cab404/ploopy-mods/headband/export/band+coils=....0+th=....2+r=...30.stl

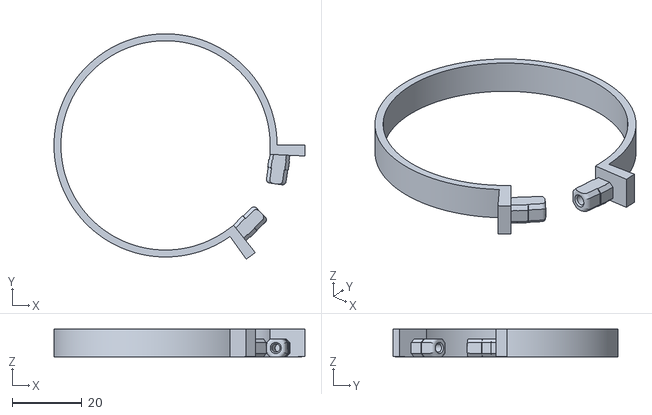
[picture p19: CAD file, 2024-08-13]
headband/export/band+coils=....0+th=....2+r=...30.stl
72.0 x 64.6 x 8.00
