cab404/ploopy-mods/headband/export/band+coils=...15+th=....2+r=...40.stl

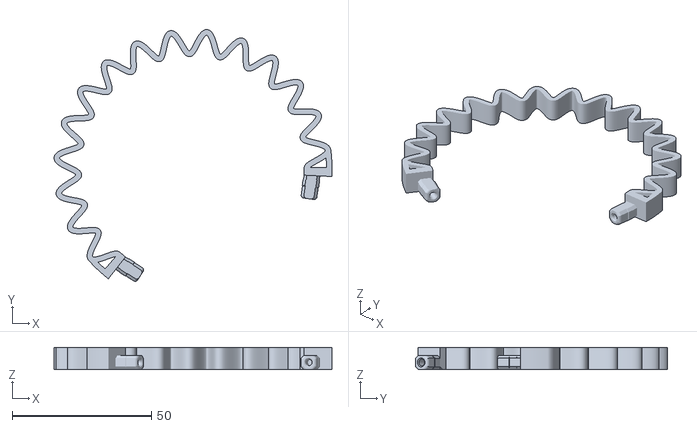
[picture p20: CAD file, 2024-08-13]
headband/export/band+coils=...15+th=....2+r=...40.stl
99.9 x 90.5 x 8.00
