cab404/ploopy-mods/headband/export/band+coils=....0+th=....2+r=...90.stl

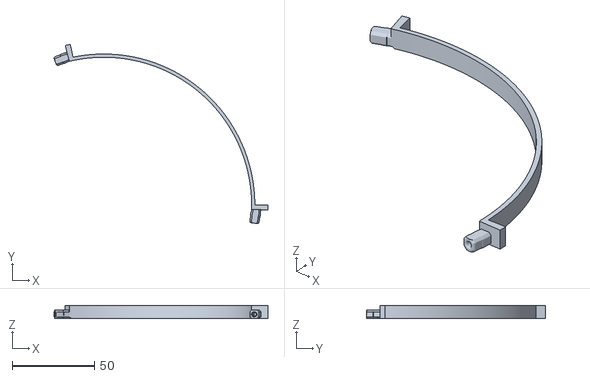
[picture p22: CAD file, 2024-08-13]
headband/export/band+coils=....0+th=....2+r=...90.stl
130.3 x 109.2 x 8.00
