cab404/ploopy-mods/headband/export/band+coils=....9+th=....2+r=...40.stl

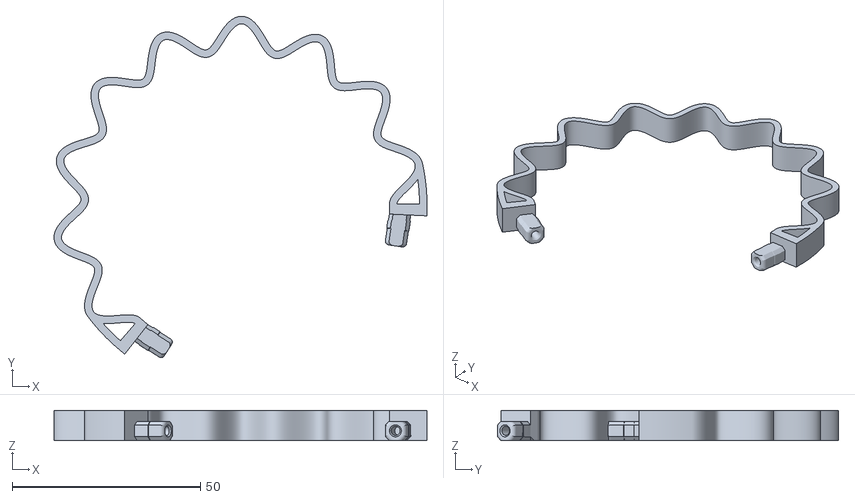
[picture p28: CAD file, 2024-08-13]
headband/export/band+coils=....9+th=....2+r=...40.stl
99.2 x 90.7 x 8.00
