cab404/ploopy-mods/headband/export/band+coils=...15+th=....4+r=...50.stl

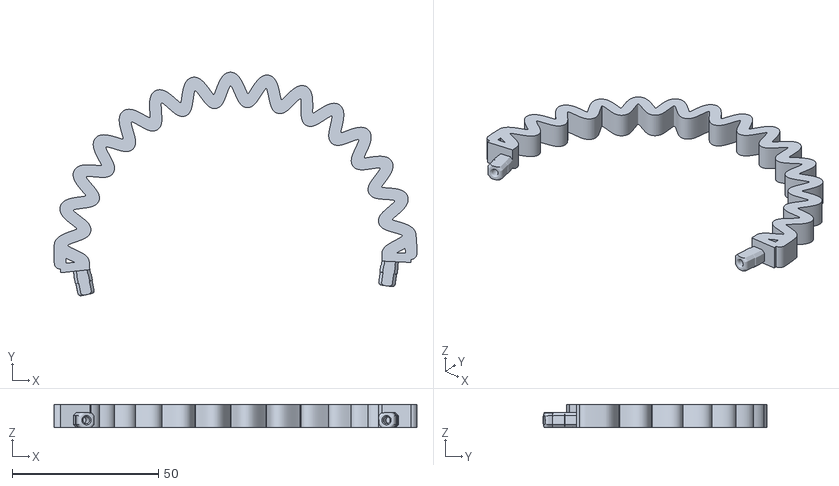
[picture p31: CAD file, 2024-08-13]
headband/export/band+coils=...15+th=....4+r=...50.stl
124.0 x 76.4 x 8.00
