cab404/ploopy-mods/headband/export/band+coils=....9+th=....2+r=...70.stl

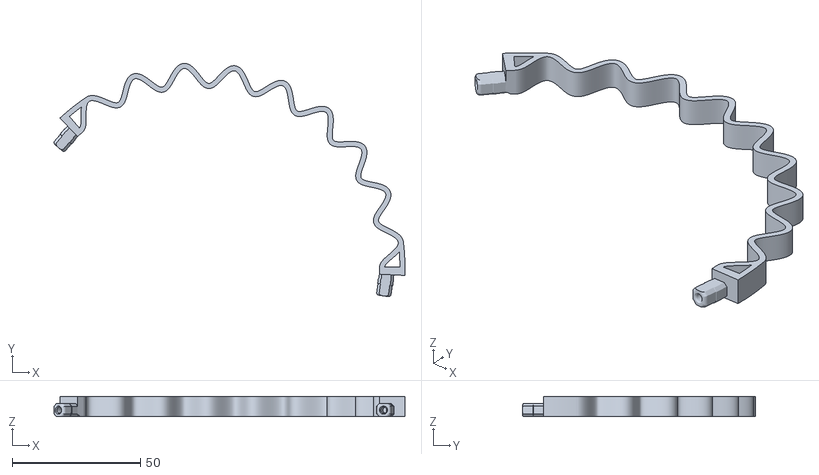
[picture p32: CAD file, 2024-08-13]
headband/export/band+coils=....9+th=....2+r=...70.stl
137.0 x 91.1 x 8.00
