cab404/ploopy-mods/newcap/export/newcap+magnet_size=..4.8+open=..yes+h=..1.9+layer_height=..0.1.stl

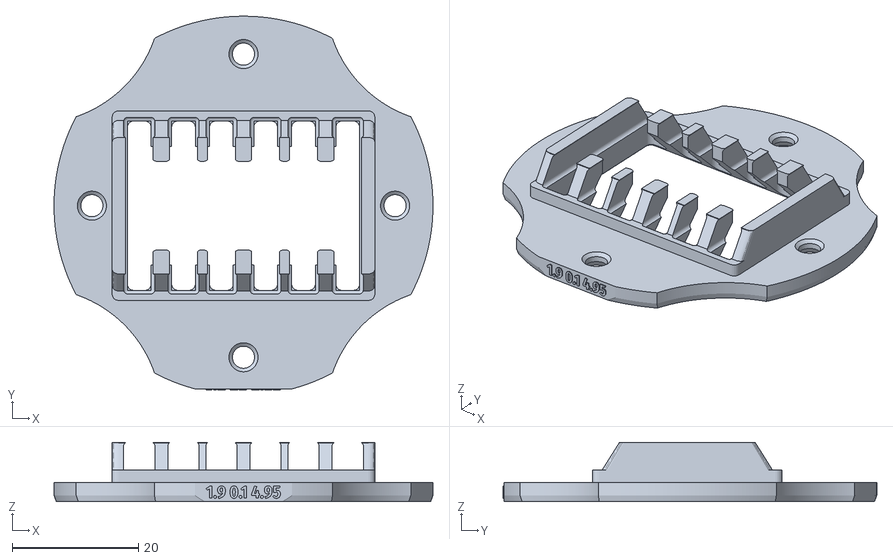
[picture p33: CAD file, 2024-08-13]
newcap/export/newcap+magnet_size=..4.8+open=..yes+h=..1.9+layer_height=..0.1.stl
60.0 x 59.1 x 9.40
