cab404/ploopy-mods/headband/export/band+coils=...15+th=....4+r=...90.stl

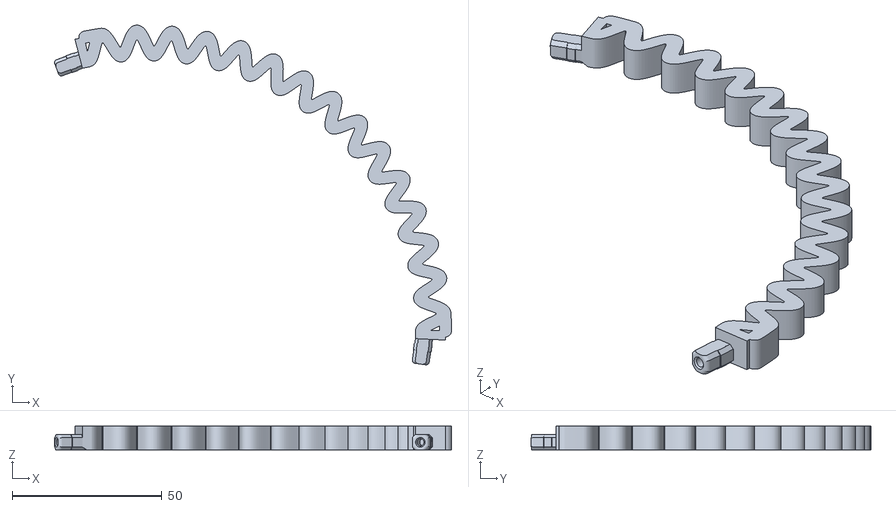
[picture p36: CAD file, 2024-08-13]
headband/export/band+coils=...15+th=....4+r=...90.stl
132.3 x 113.3 x 8.00
