cab404/ploopy-mods/headband/export/band+coils=....9+th=....4+r=...70.stl

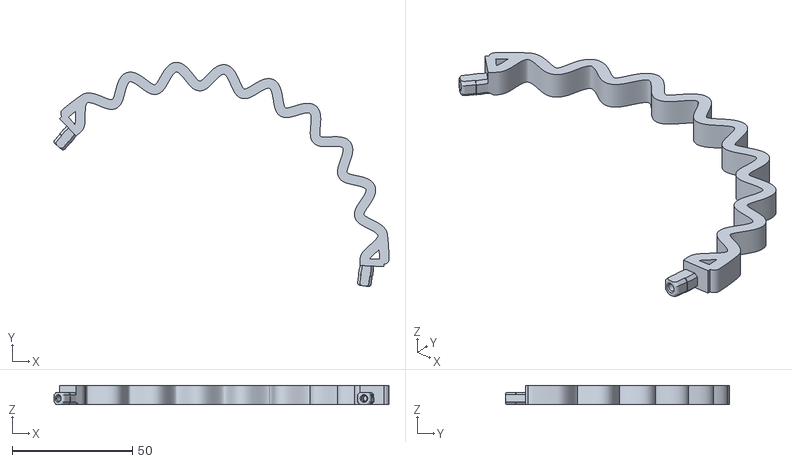
[picture p38: CAD file, 2024-08-13]
headband/export/band+coils=....9+th=....4+r=...70.stl
139.0 x 93.1 x 8.00
