cab404/ploopy-mods/headband/export/band+coils=....5+th=....2+r=...40.stl

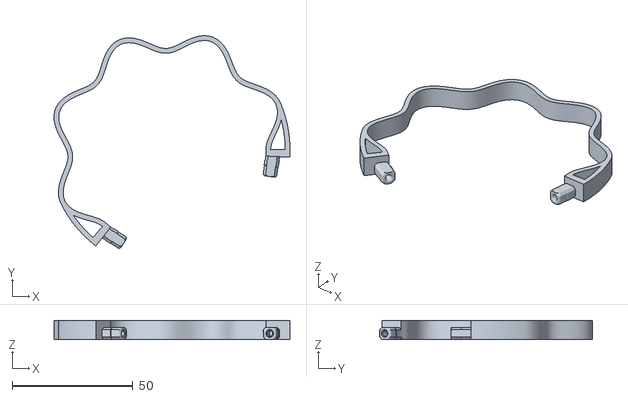
[picture p39: CAD file, 2024-08-13]
headband/export/band+coils=....5+th=....2+r=...40.stl
97.7 x 88.0 x 8.00
