cab404/ploopy-mods/newcap/export/newcap+magnet_size=..4.5+open=..yes+h=..1.8+layer_height=..0.2.stl

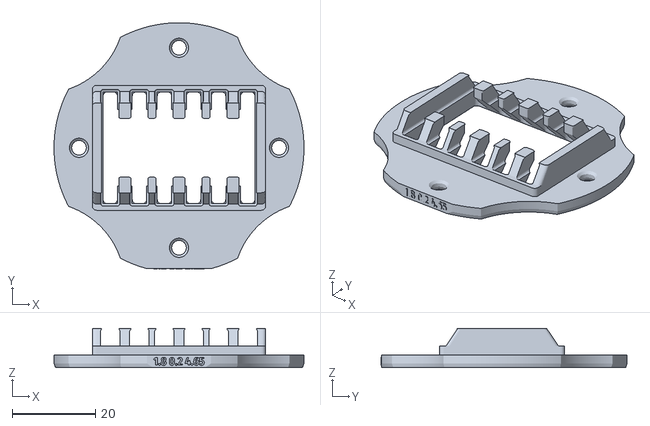
[picture p40: CAD file, 2024-08-13]
newcap/export/newcap+magnet_size=..4.5+open=..yes+h=..1.8+layer_height=..0.2.stl
60.0 x 59.1 x 9.40
