cab404/ploopy-mods/headband/export/band+coils=....1+th=....2+r=...30.stl

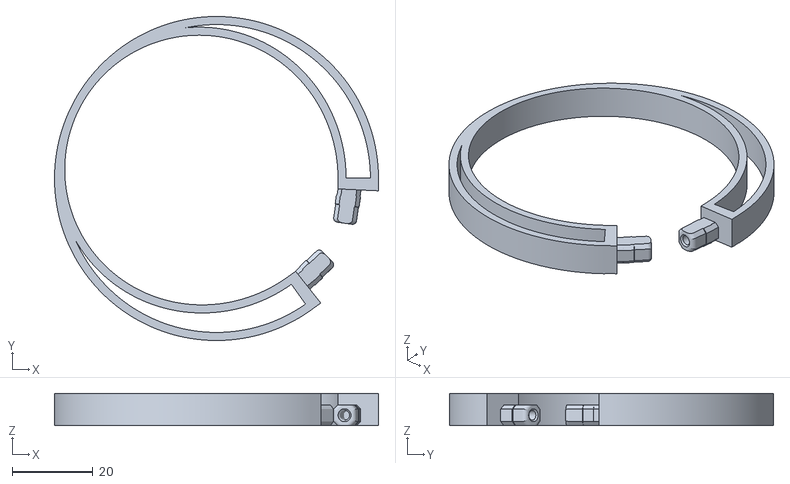
[picture p41: CAD file, 2024-08-13]
headband/export/band+coils=....1+th=....2+r=...30.stl
80.0 x 80.0 x 8.00
