cab404/ploopy-mods/headband/export/band+coils=....9+th=....2+r=...50.stl

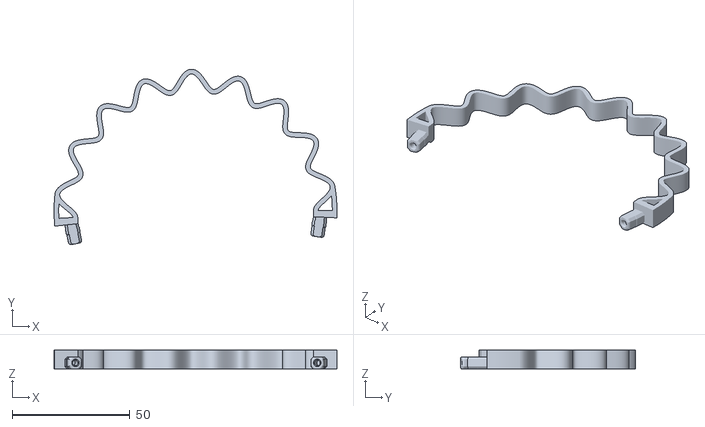
[picture p42: CAD file, 2024-08-13]
headband/export/band+coils=....9+th=....2+r=...50.stl
120.0 x 74.4 x 8.00
