cab404/ploopy-mods/newcap/export/newcap+magnet_size=..4.5+open=..yes+h=..1.6+layer_height=..0.1.stl

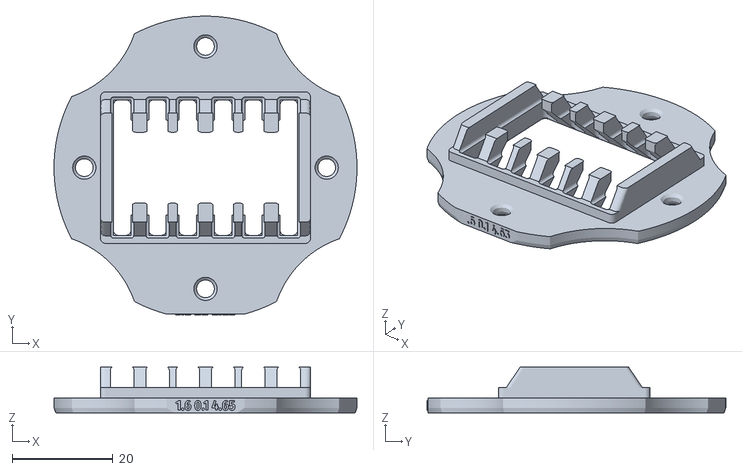
[picture p43: CAD file, 2024-08-13]
newcap/export/newcap+magnet_size=..4.5+open=..yes+h=..1.6+layer_height=..0.1.stl
60.0 x 59.1 x 9.10
