cab404/ploopy-mods/headband/export/band+coils=....5+th=....2+r=...70.stl

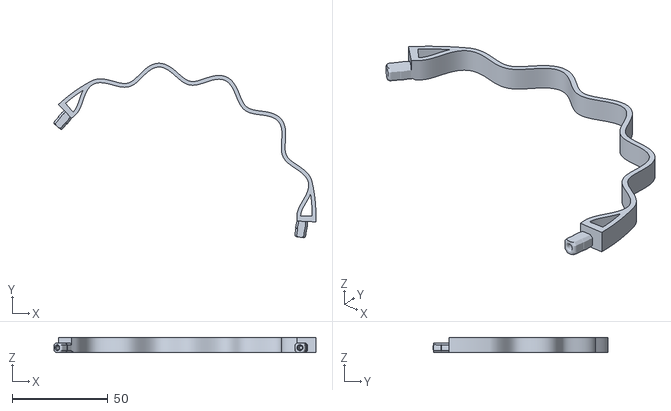
[picture p44: CAD file, 2024-08-13]
headband/export/band+coils=....5+th=....2+r=...70.stl
137.0 x 91.3 x 8.00
