cab404/ploopy-mods/headband/export/band+coils=....0+th=....2+r=...40.stl

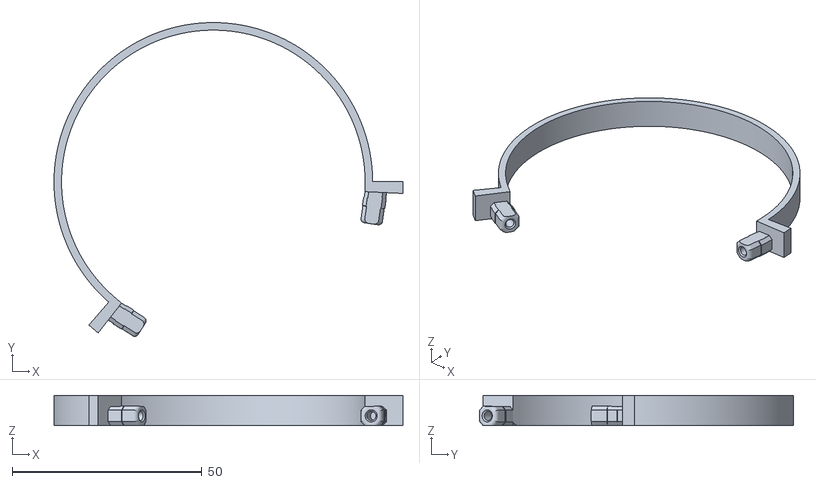
[picture p45: CAD file, 2024-08-13]
headband/export/band+coils=....0+th=....2+r=...40.stl
92.0 x 82.7 x 8.00
