cab404/ploopy-mods/headband/export/band+coils=....0+th=....2+r=...50.stl

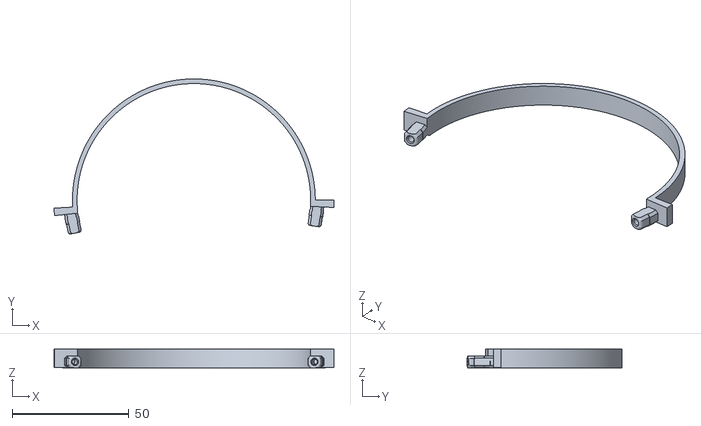
[picture p47: CAD file, 2024-08-13]
headband/export/band+coils=....0+th=....2+r=...50.stl
119.9 x 66.4 x 8.00
