cab404/ploopy-mods/headband/export/band+coils=....1+th=....4+r=...70.stl

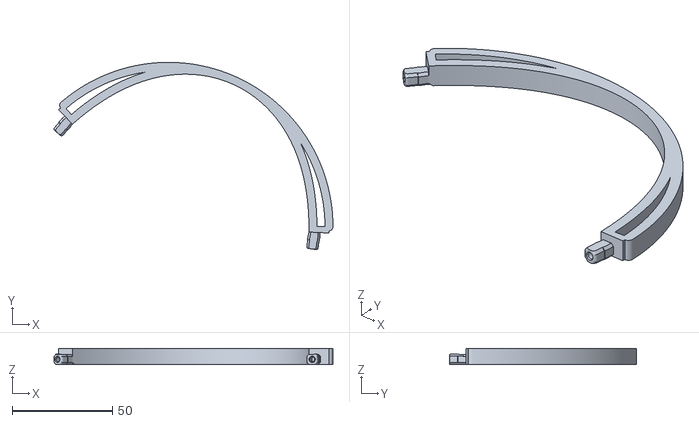
[picture p49: CAD file, 2024-08-13]
headband/export/band+coils=....1+th=....4+r=...70.stl
139.0 x 93.3 x 8.00
