cab404/ploopy-mods/headband/export/band+coils=....9+th=....2+r=...30.stl

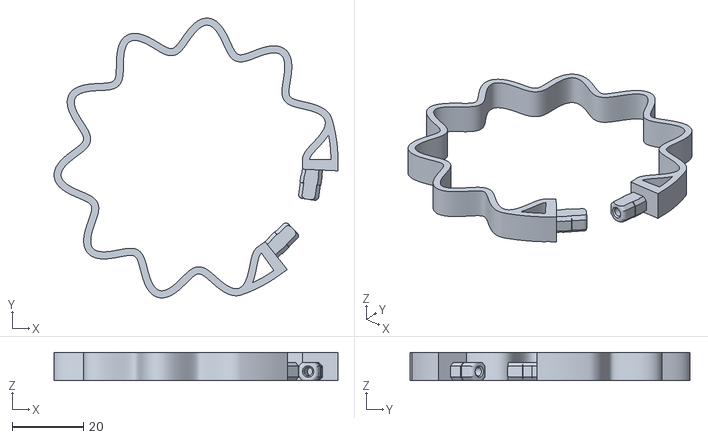
[picture p51: CAD file, 2024-08-13]
headband/export/band+coils=....9+th=....2+r=...30.stl
79.8 x 78.6 x 8.00
