cab404/ploopy-mods/headband/export/band+coils=....9+th=....4+r=...30.stl

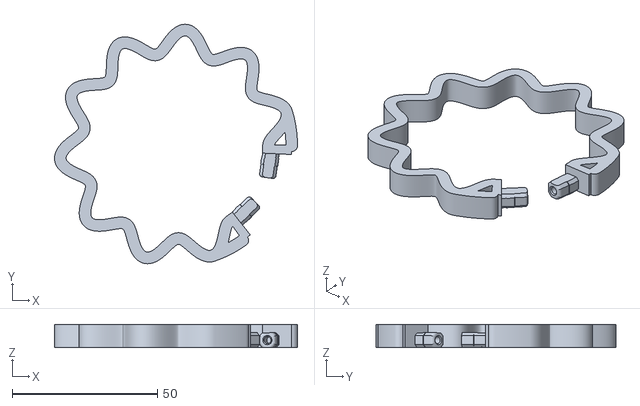
[picture p52: CAD file, 2024-08-13]
headband/export/band+coils=....9+th=....4+r=...30.stl
83.7 x 82.5 x 8.00
