cab404/ploopy-mods/headband/export/band+coils=...15+th=....2+r=...30.stl

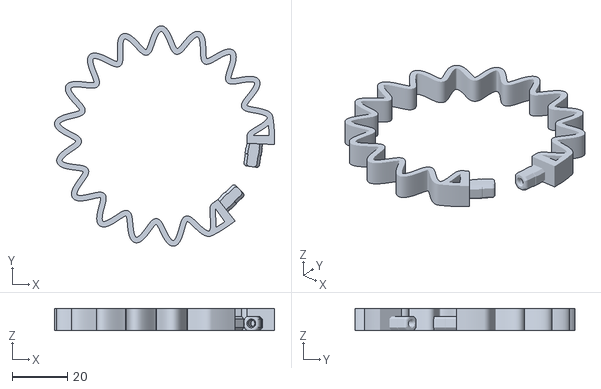
[picture p54: CAD file, 2024-08-13]
headband/export/band+coils=...15+th=....2+r=...30.stl
79.7 x 79.8 x 8.00
