cab404/ploopy-mods/headband/export/band+coils=....0+th=....4+r=...50.stl

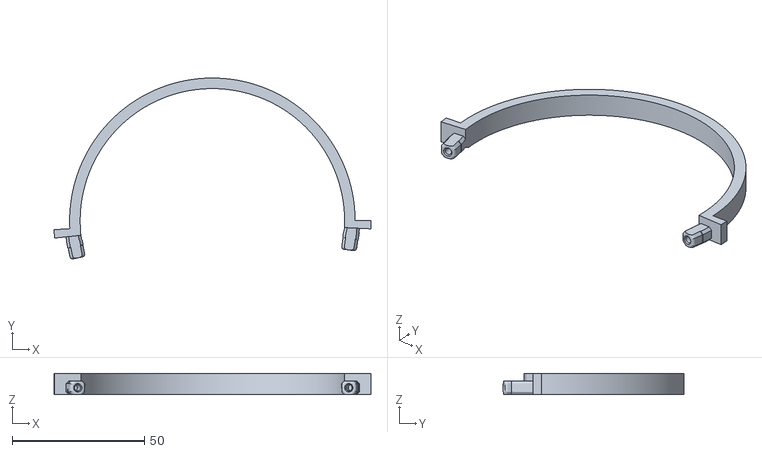
[picture p55: CAD file, 2024-08-13]
headband/export/band+coils=....0+th=....4+r=...50.stl
119.9 x 68.4 x 8.00
