cab404/ploopy-mods/headband/export/band+coils=....9+th=....2+r=...90.stl

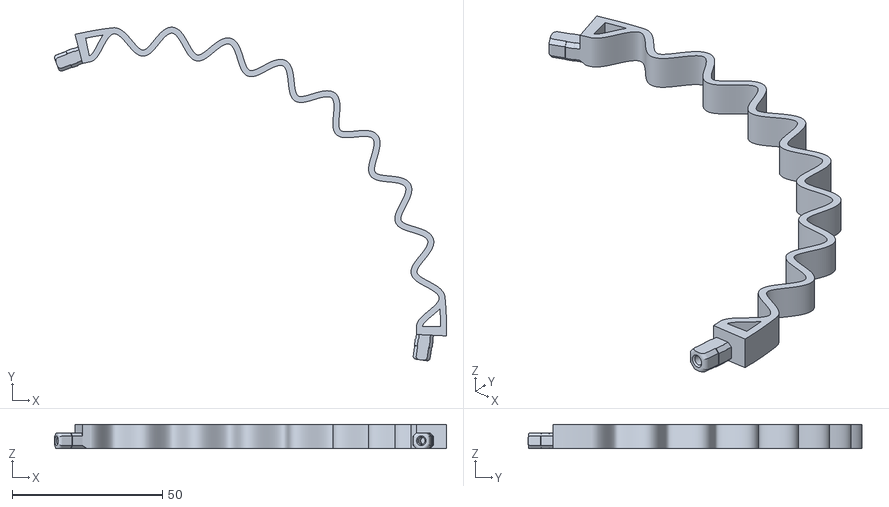
[picture p56: CAD file, 2024-08-13]
headband/export/band+coils=....9+th=....2+r=...90.stl
130.3 x 110.9 x 8.00
