cab404/ploopy-mods/headband/export/band+coils=....1+th=....2+r=...40.stl

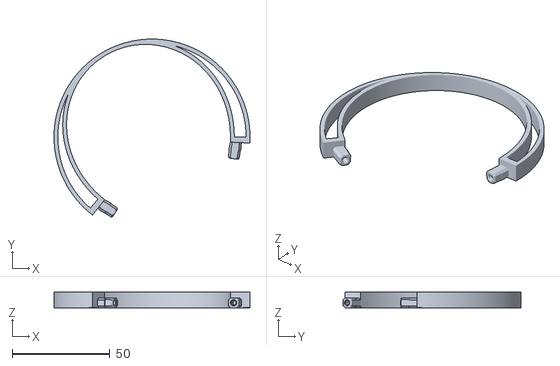
[picture p58: CAD file, 2024-08-13]
headband/export/band+coils=....1+th=....2+r=...40.stl
100.0 x 90.7 x 8.00
