cab404/ploopy-mods/headband/export/band+coils=....1+th=....4+r=...40.stl

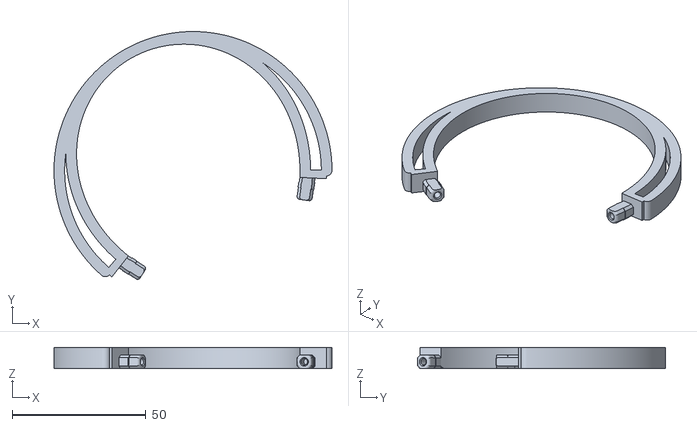
[picture p60: CAD file, 2024-08-13]
headband/export/band+coils=....1+th=....4+r=...40.stl
104.0 x 92.7 x 8.00
