cab404/ploopy-mods/headband/export/band+coils=....5+th=....2+r=...30.stl

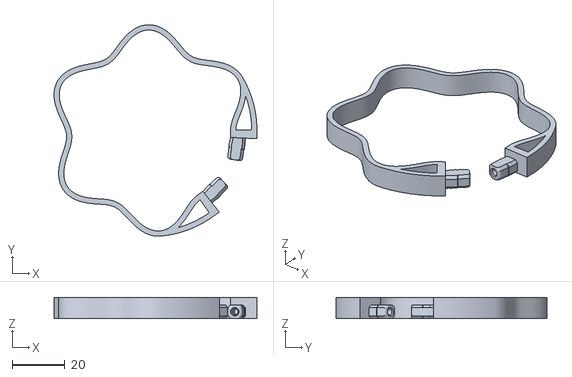
[picture p63: CAD file, 2024-08-13]
headband/export/band+coils=....5+th=....2+r=...30.stl
76.7 x 79.9 x 8.00
