cab404/ploopy-mods/headband/export/band+coils=....9+th=....4+r=...40.stl

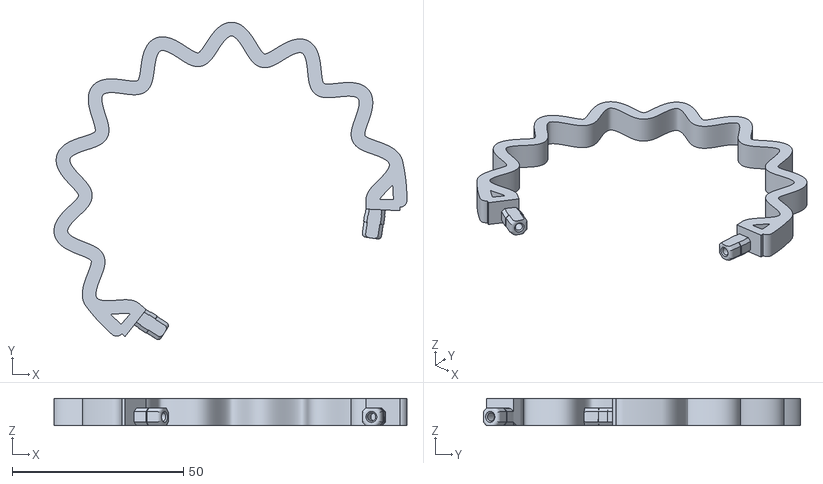
[picture p65: CAD file, 2024-08-13]
headband/export/band+coils=....9+th=....4+r=...40.stl
103.1 x 92.7 x 8.00
