cab404/ploopy-mods/headband/export/band+coils=....5+th=....4+r=...40.stl

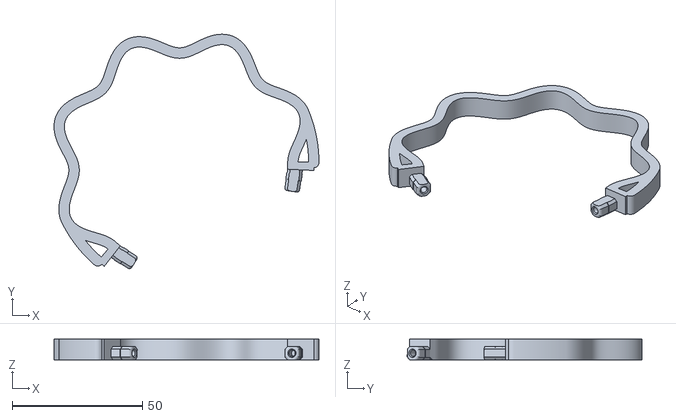
[picture p67: CAD file, 2024-08-13]
headband/export/band+coils=....5+th=....4+r=...40.stl
101.6 x 89.9 x 8.00
