cab404/ploopy-mods/headband/export/band+coils=...15+th=....4+r=...40.stl

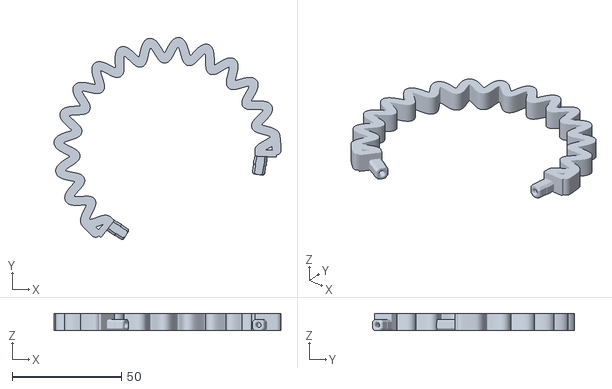
[picture p68: CAD file, 2024-08-13]
headband/export/band+coils=...15+th=....4+r=...40.stl
103.9 x 92.5 x 8.00
