cab404/ploopy-mods/headband/export/band+coils=....5+th=....4+r=...30.stl

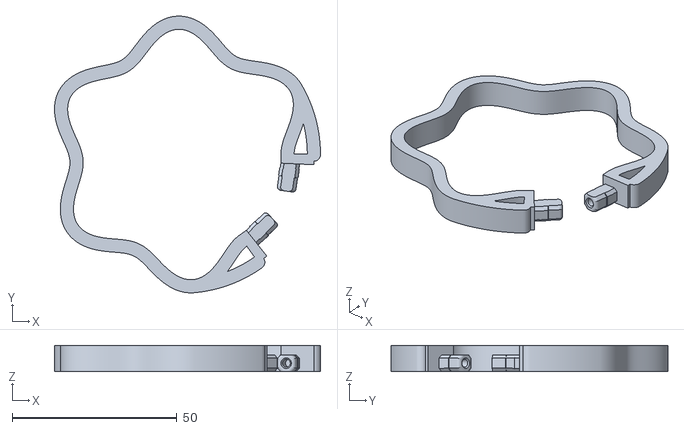
[picture p69: CAD file, 2024-08-13]
headband/export/band+coils=....5+th=....4+r=...30.stl
80.6 x 83.9 x 8.00
