cab404/ploopy-mods/headband/export/band+coils=....0+th=....4+r=...70.stl

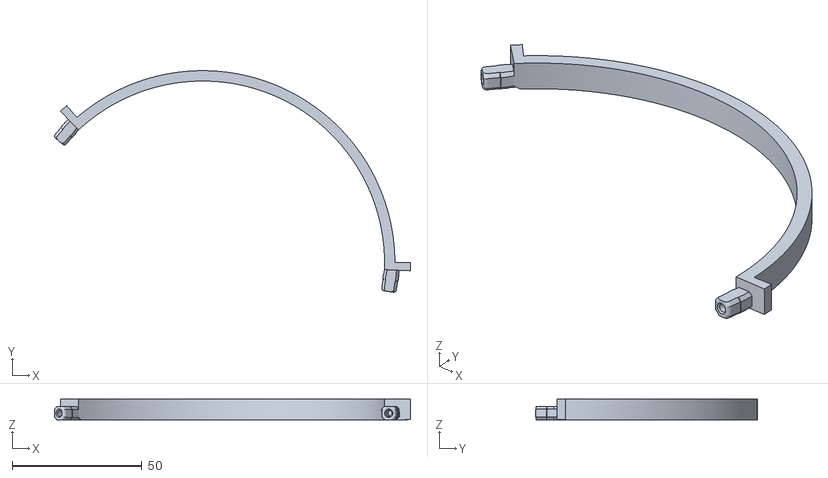
[picture p71: CAD file, 2024-08-13]
headband/export/band+coils=....0+th=....4+r=...70.stl
137.0 x 85.3 x 8.00
