cab404/ploopy-mods/headband/export/band+coils=....0+th=....4+r=...30.stl

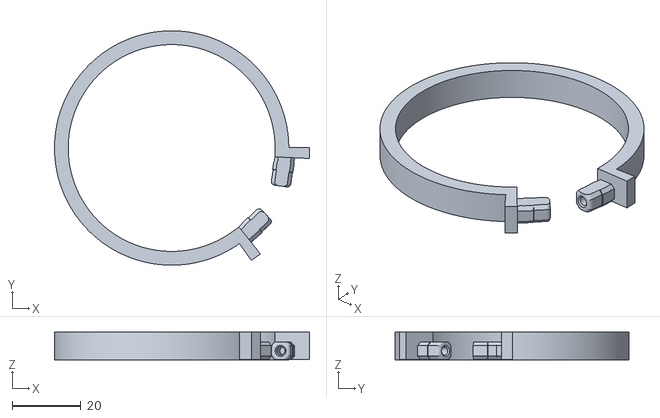
[picture p72: CAD file, 2024-08-13]
headband/export/band+coils=....0+th=....4+r=...30.stl
74.0 x 68.0 x 8.00
